jacobtohahn/ZTO-80/PCB/SBC/v3.1/PDF/SBC3.1_PCB.pdf

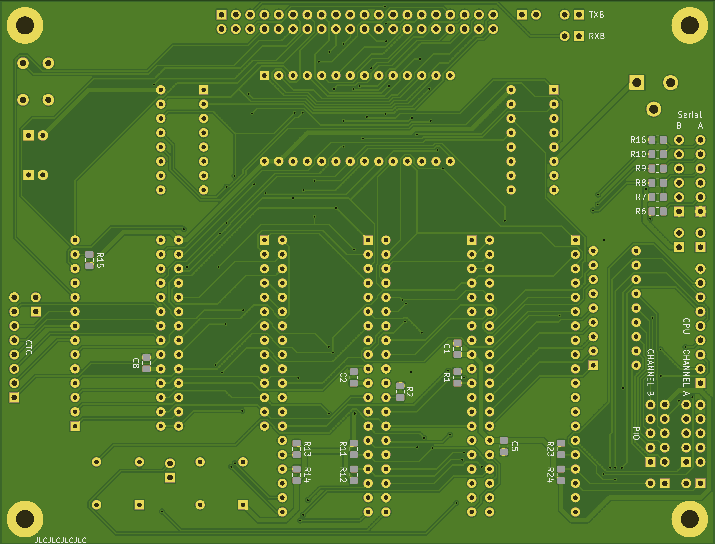
[picture p14: page 1]
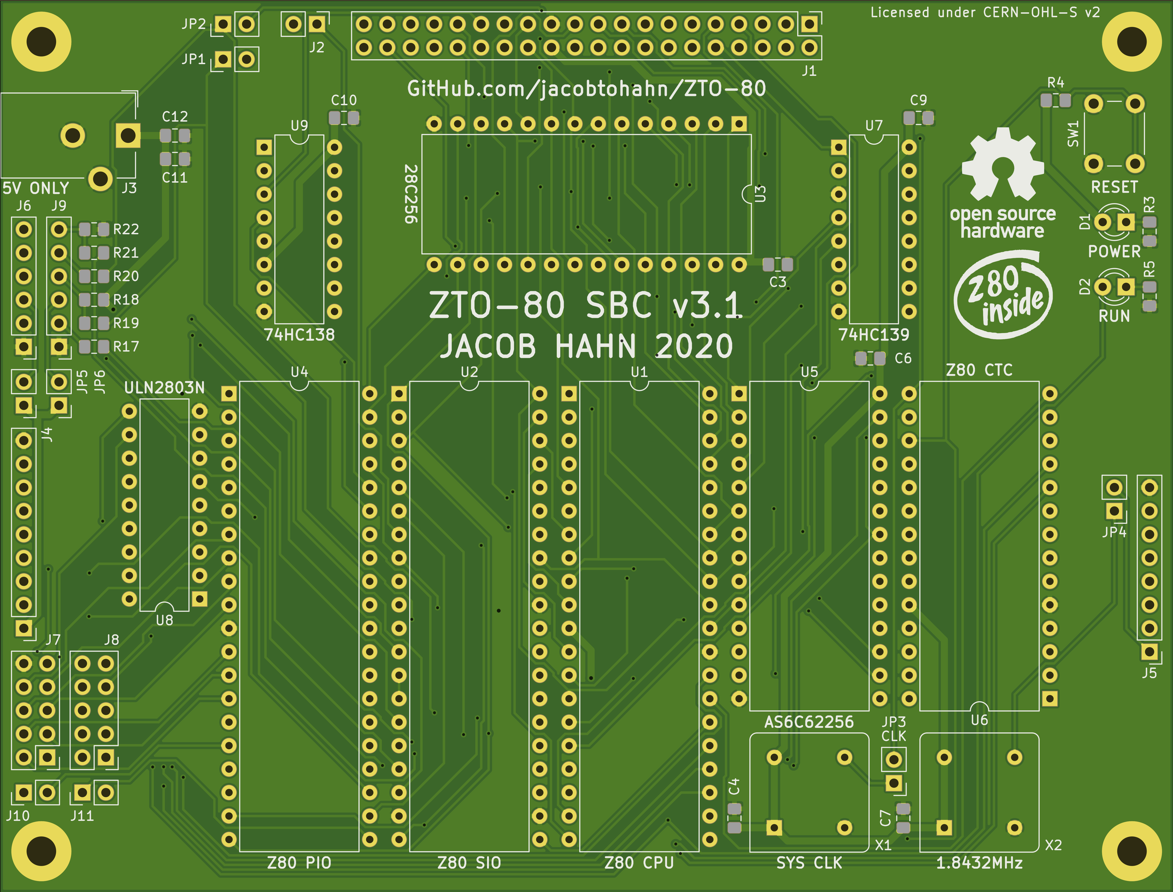
[picture p15: page 2]
