jacobtohahn/ZTO-80/Images/Backplane1.jpg

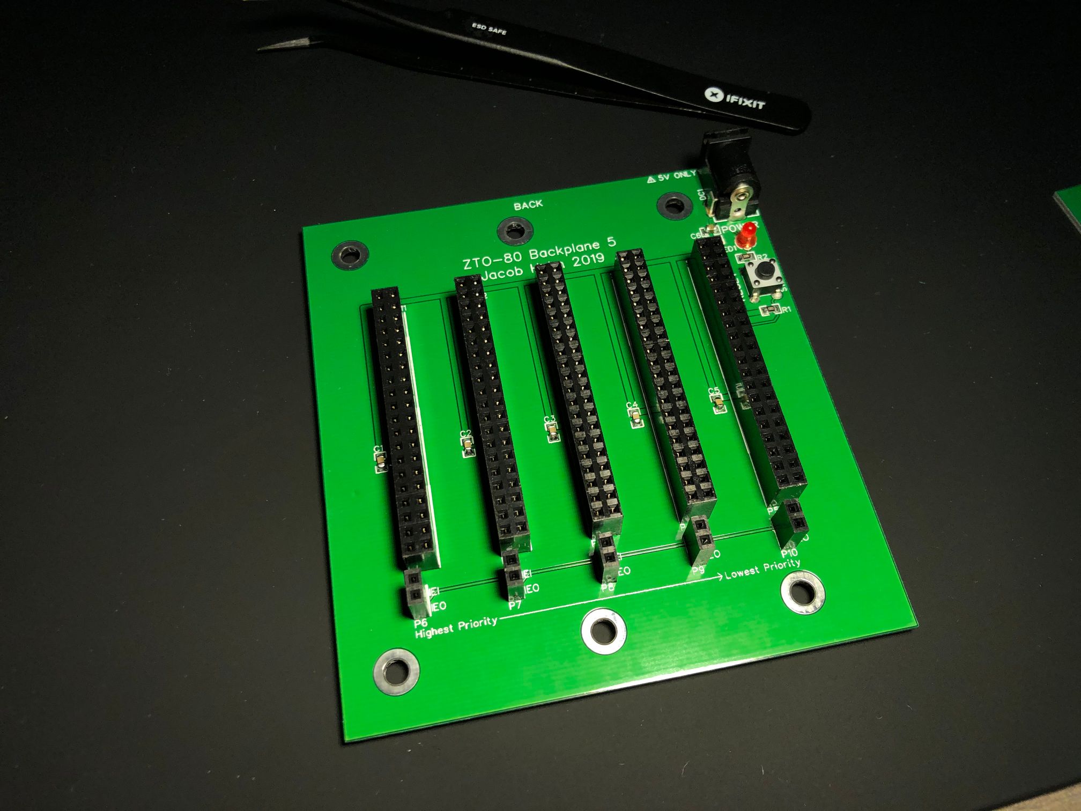
Images/Backplane1.jpg
