jacobtohahn/ZTO-80/Images/CPU.jpg

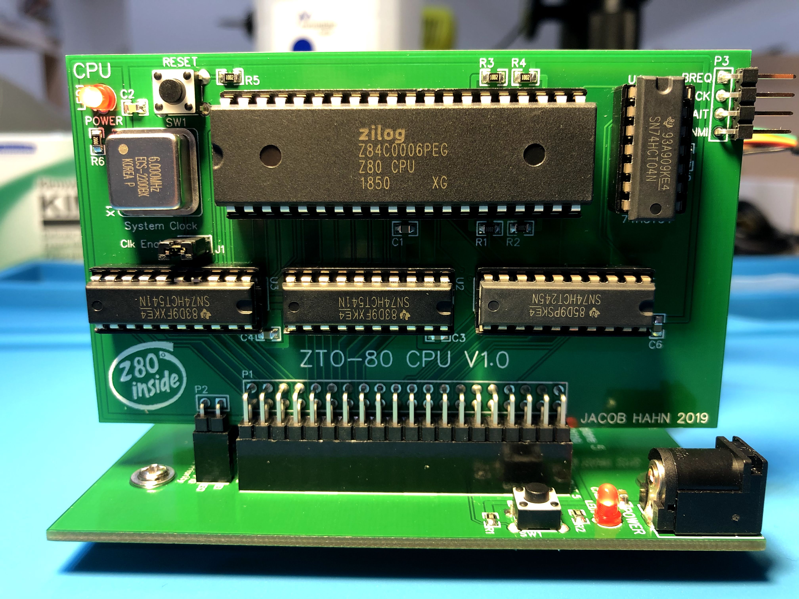
Images/CPU.jpg
