jacobtohahn/ZTO-80/Images/Memory.jpg

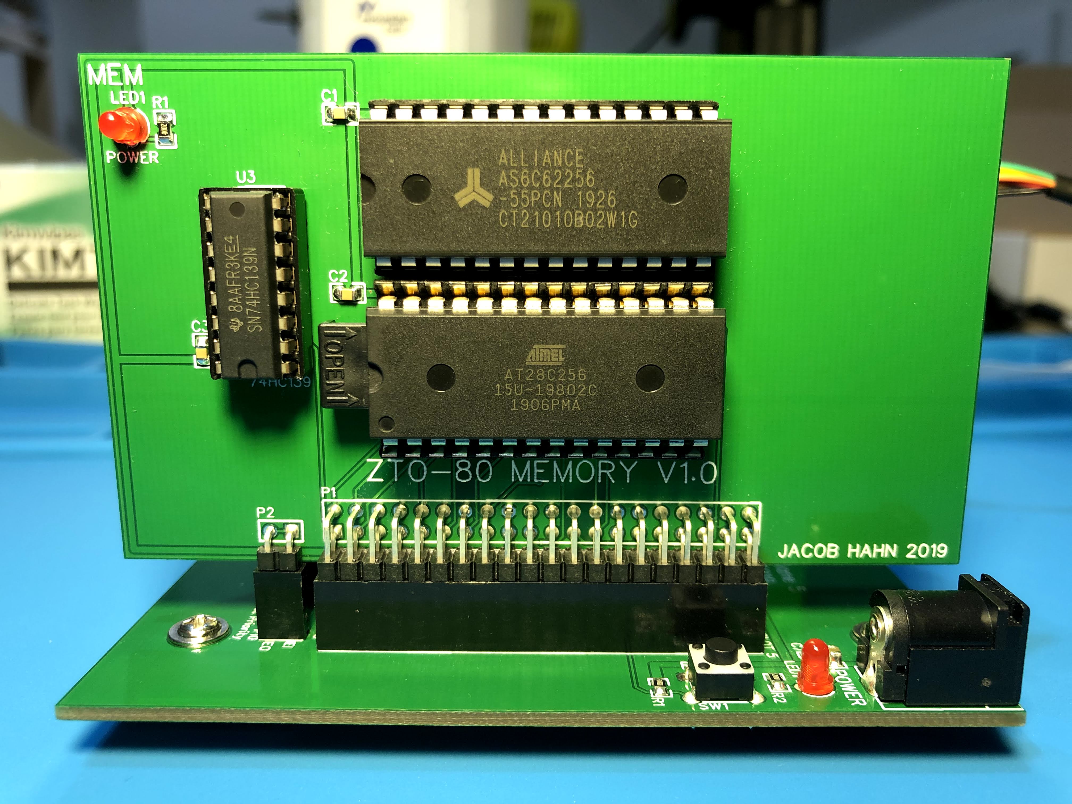
Images/Memory.jpg
