jacobtohahn/ZTO-80/PCB/Modular System/ZTO-80 SIO/PDF/SIO_sch.pdf

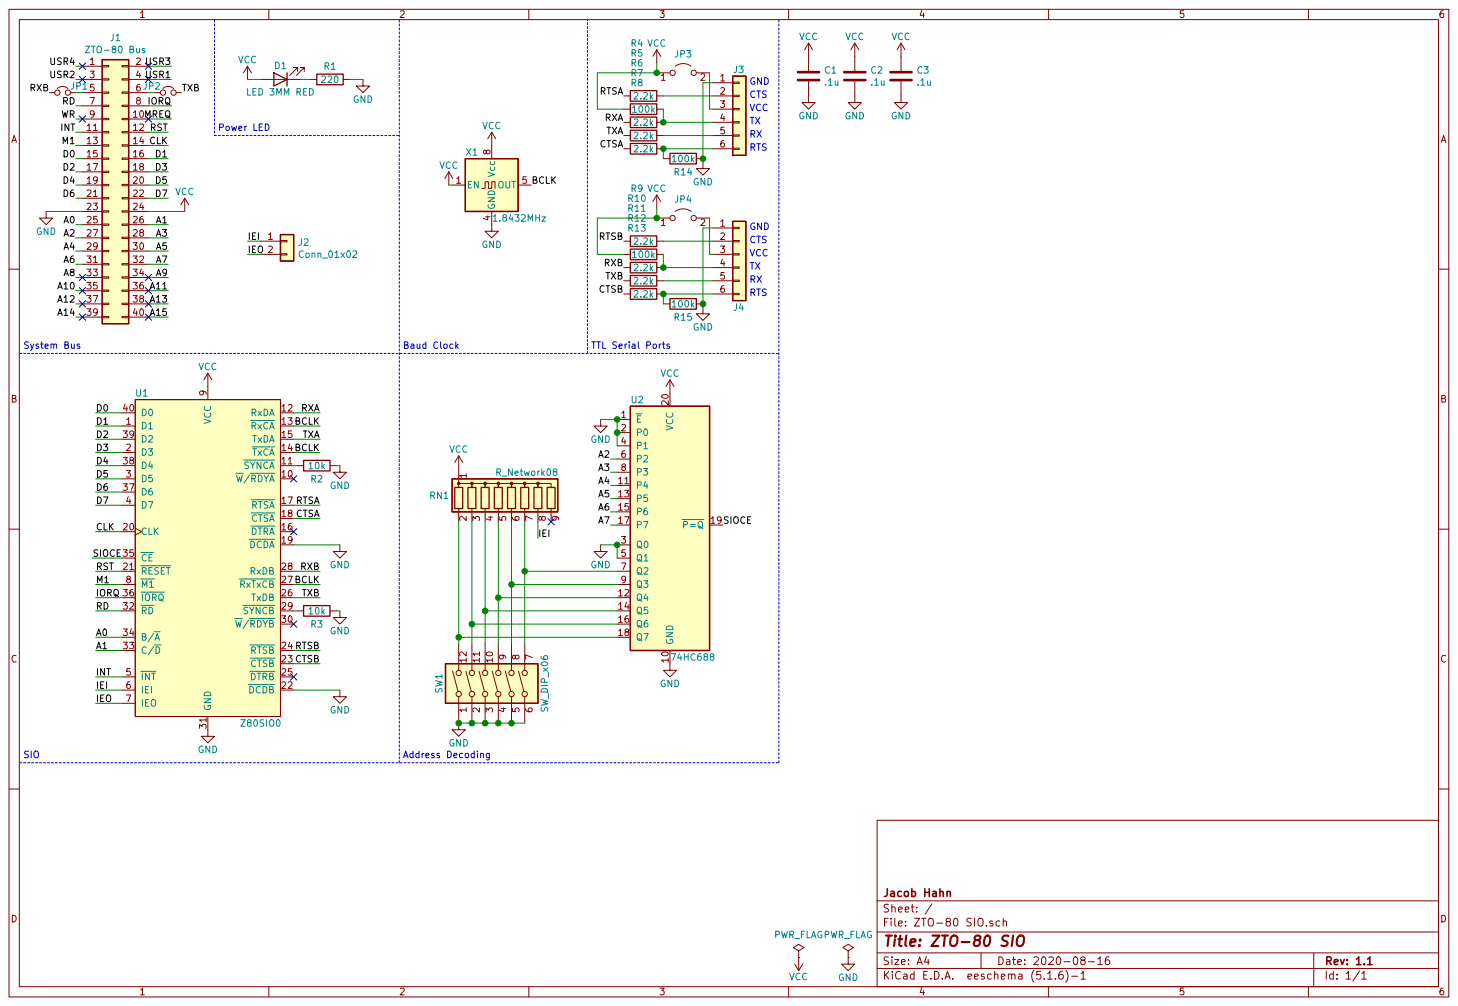
[picture p38: page 1]

Baud Clock Power LED

File: ZTO-80 SIO.sch Sheet: / Jacob Hahn

Id: 1/1 Title: ZTO-80 SIO
